FredThx/FERG/divers/arduino.PNG

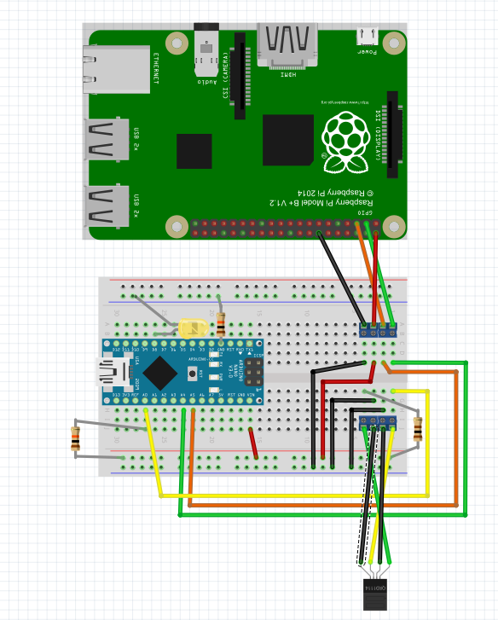
divers/arduino.PNG
