FredThx/FERG/divers/carte.png

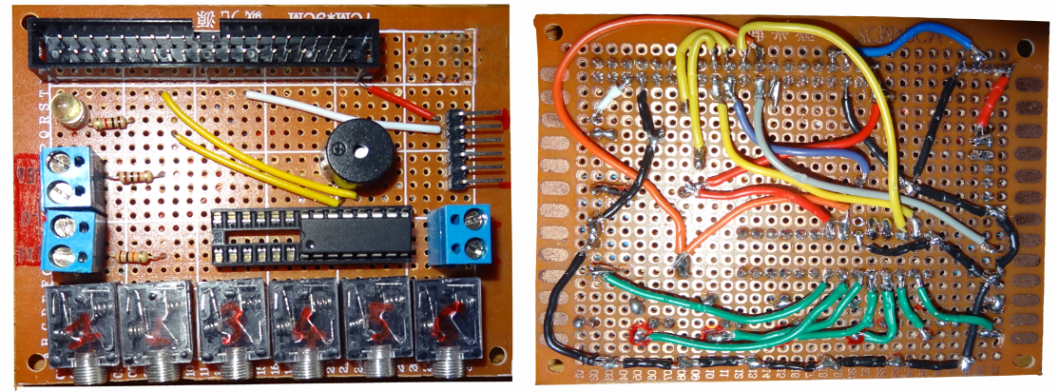
divers/carte.png
