FredThx/FERG/divers/detecteur_tension.jpg

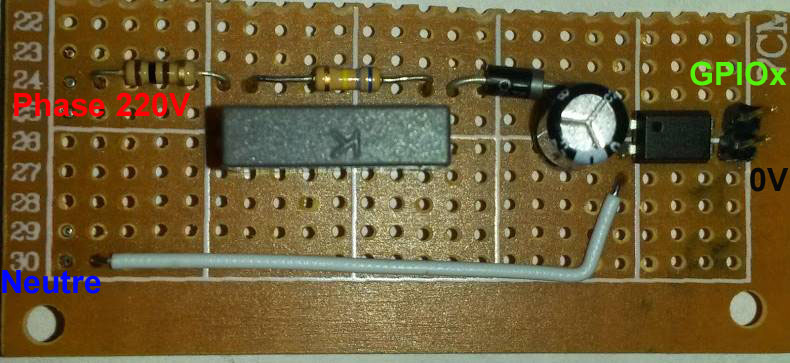
divers/detecteur_tension.jpg
