FredThx/FERG/divers/detection_secteur.png

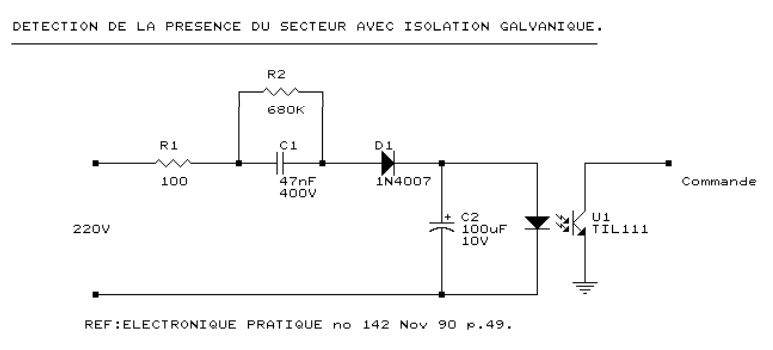
divers/detection_secteur.png
