FredThx/FERG/divers/DSC08218.png

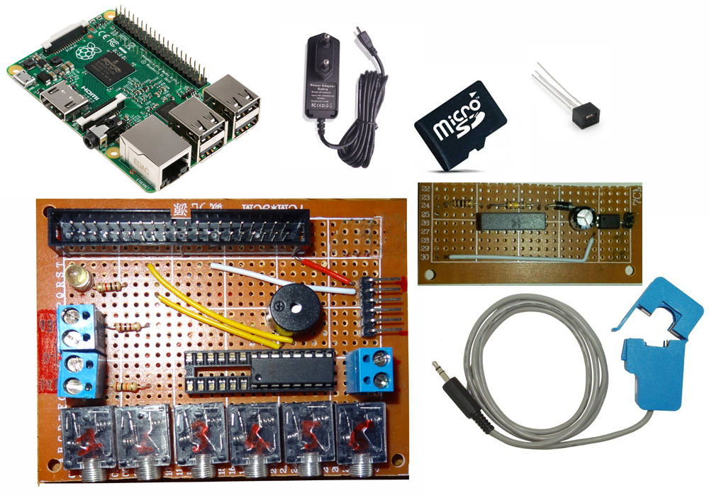
divers/DSC08218.png
