FredThx/FERG/divers/DSC08221.JPG

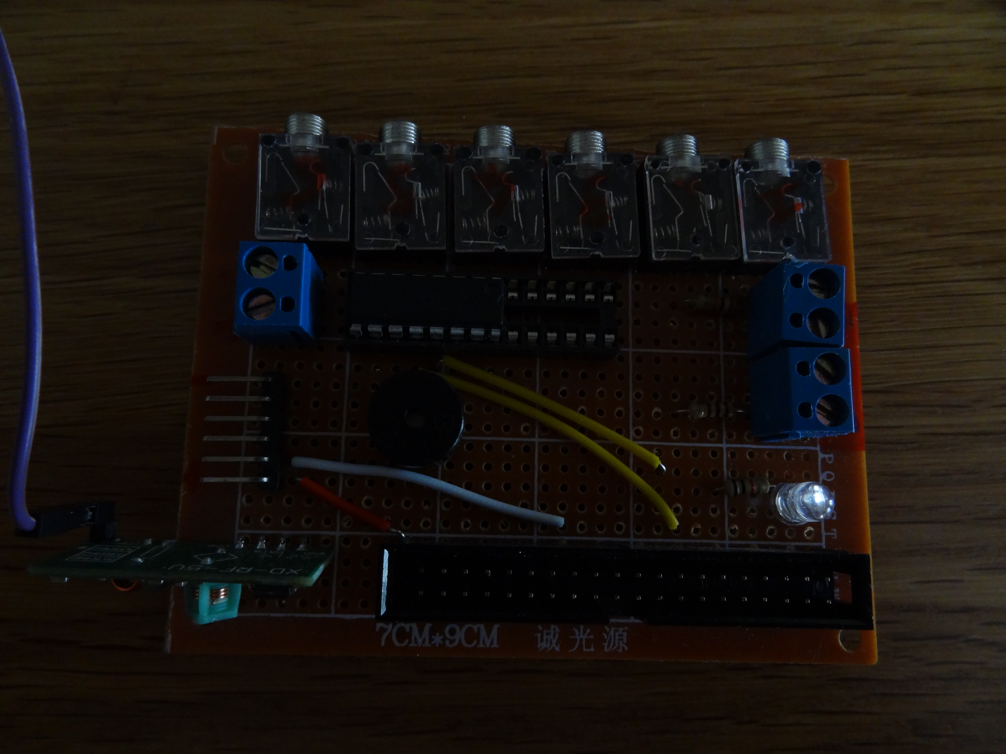
divers/DSC08221.JPG
