FredThx/FERG/divers/DSC09356.png

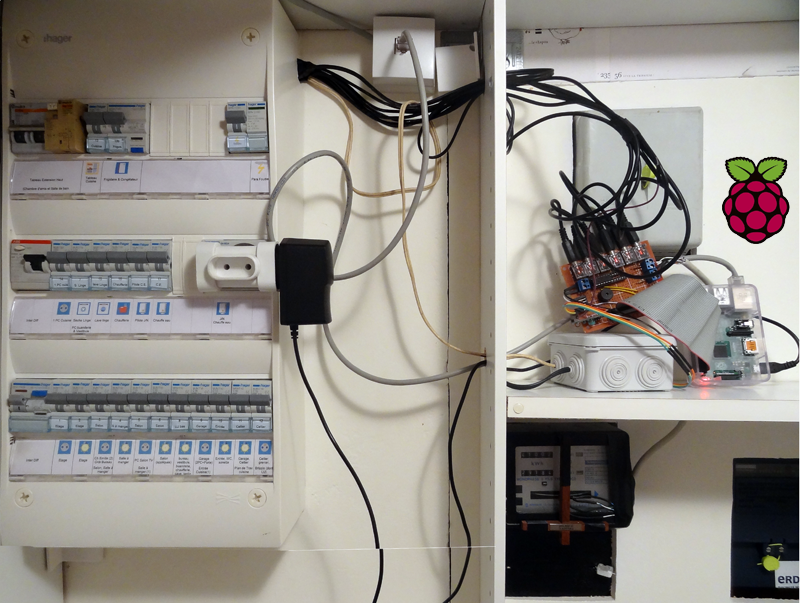
divers/DSC09356.png
