FredThx/FERG/divers/DSC09357.JPG

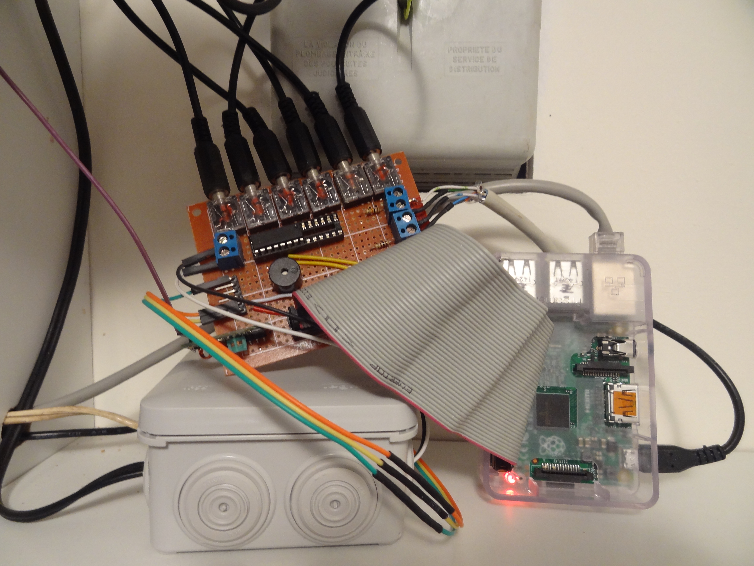
divers/DSC09357.JPG
