FredThx/FERG/divers/DSC09358.JPG

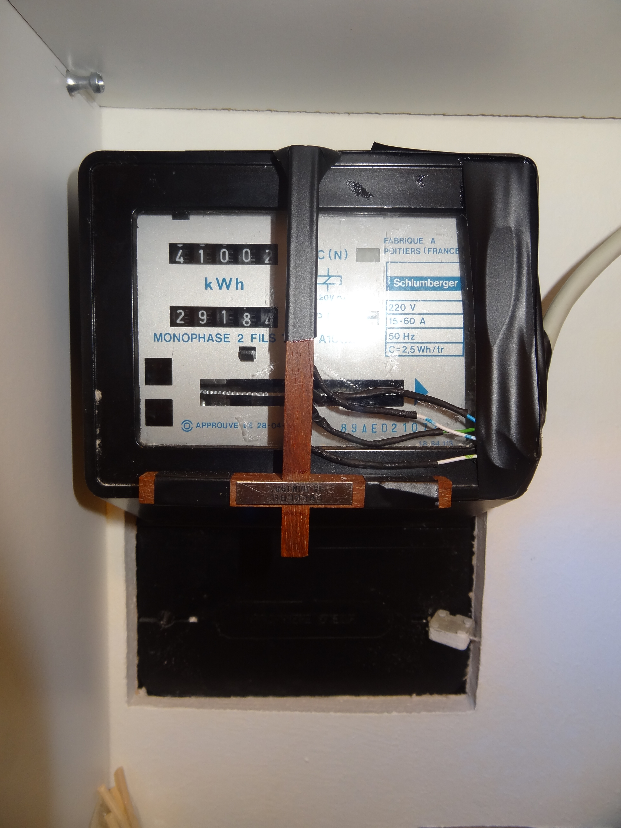
divers/DSC09358.JPG
