FredThx/FERG/divers/DSC09360.JPG

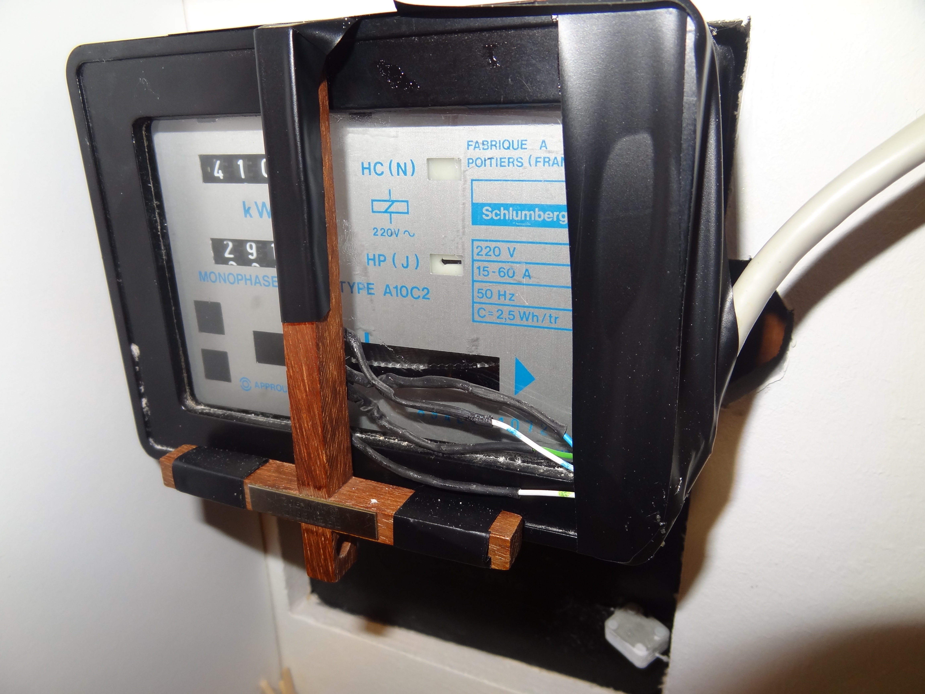
divers/DSC09360.JPG
