FredThx/FERG/divers/FERG sauf 433_circuit imprimé.png

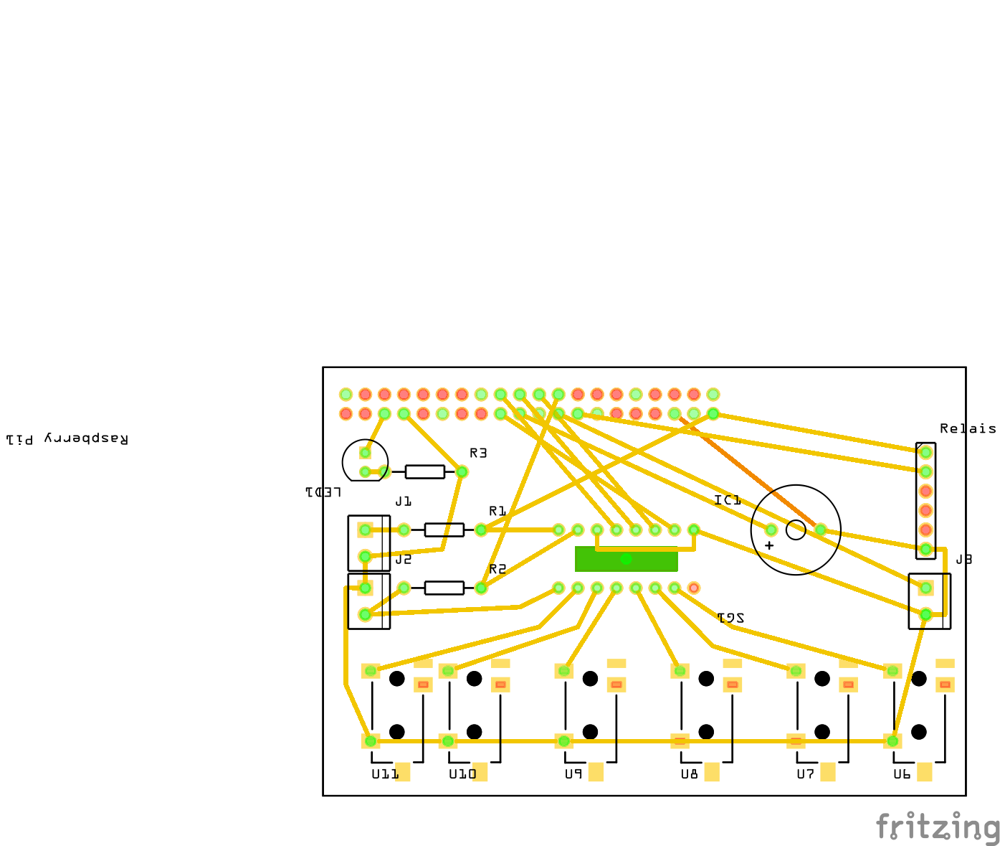
divers/FERG sauf 433_circuit imprimé.png
