FredThx/FERG/divers/FERG sauf 433_schéma.png

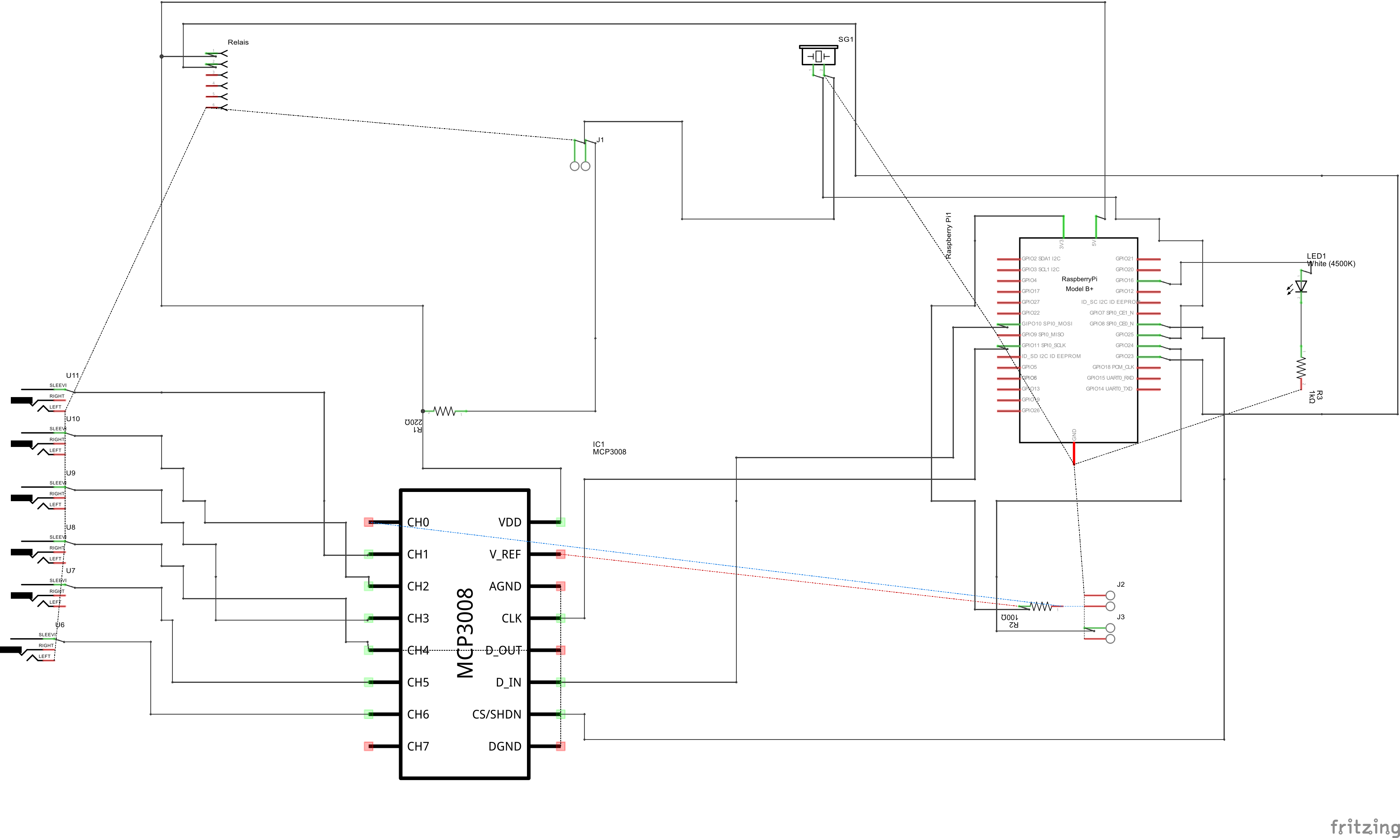
divers/FERG sauf 433_schéma.png
