FredThx/FERG/divers/FERG.JPG

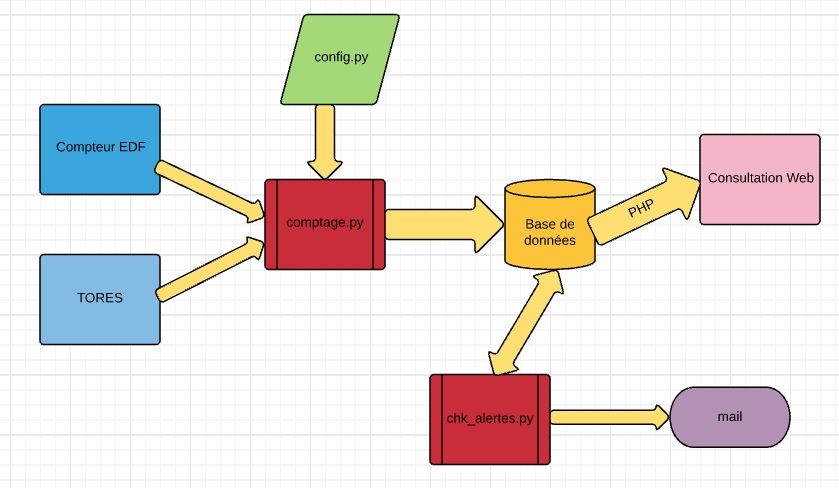
divers/FERG.JPG
