FredThx/FERG/divers/mcp3008.png

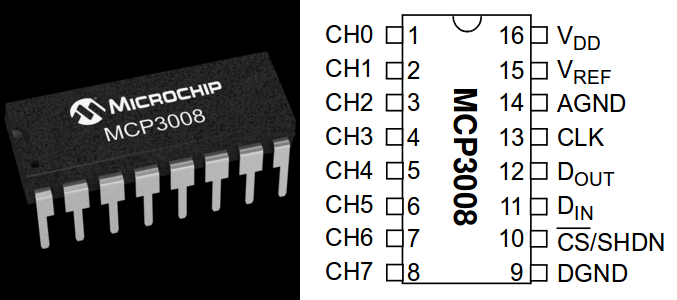
divers/mcp3008.png
