FredThx/FERG/divers/plexo.png

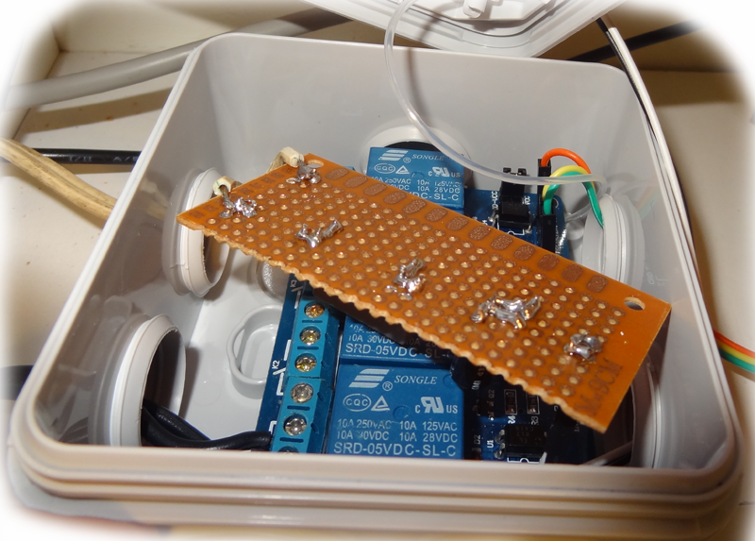
divers/plexo.png
