FredThx/FERG/divers/raspberry.png

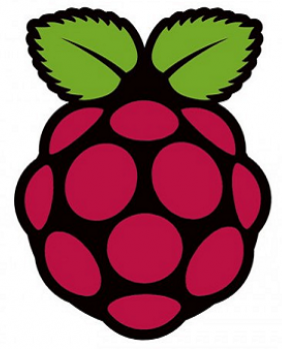
divers/raspberry.png
