FredThx/FERG/divers/relais.jpg

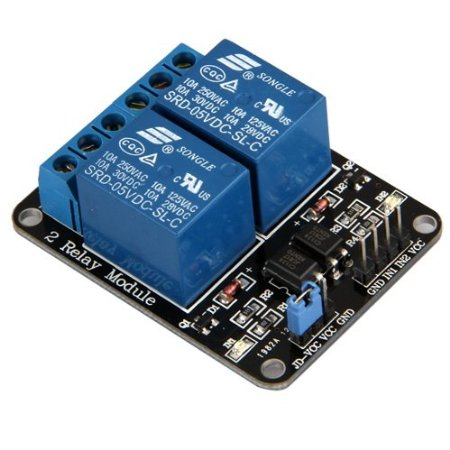
divers/relais.jpg
