FredThx/FERG/divers/synology.png

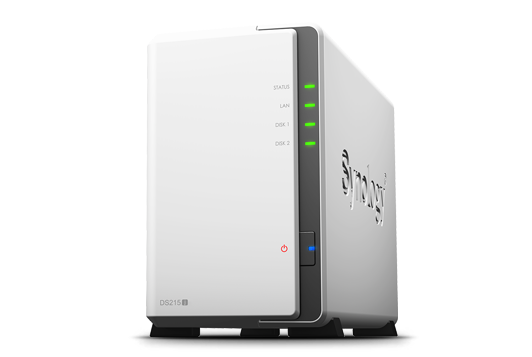
divers/synology.png
