FredThx/FERG/divers/tableau.png

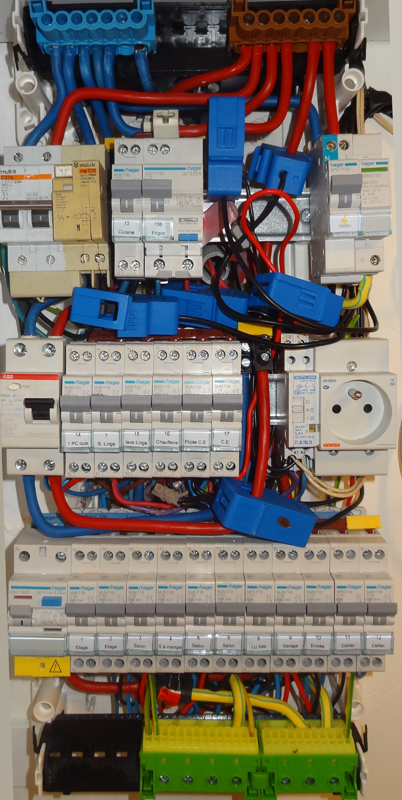
divers/tableau.png
