FredThx/FERG/divers/tore.png

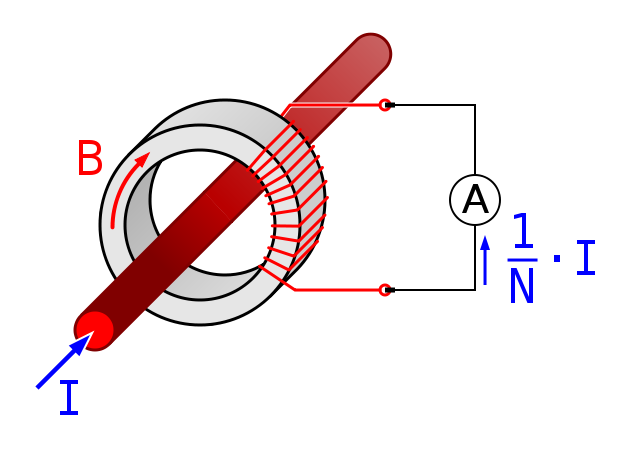
divers/tore.png
