FredThx/FERG/divers/web2.JPG

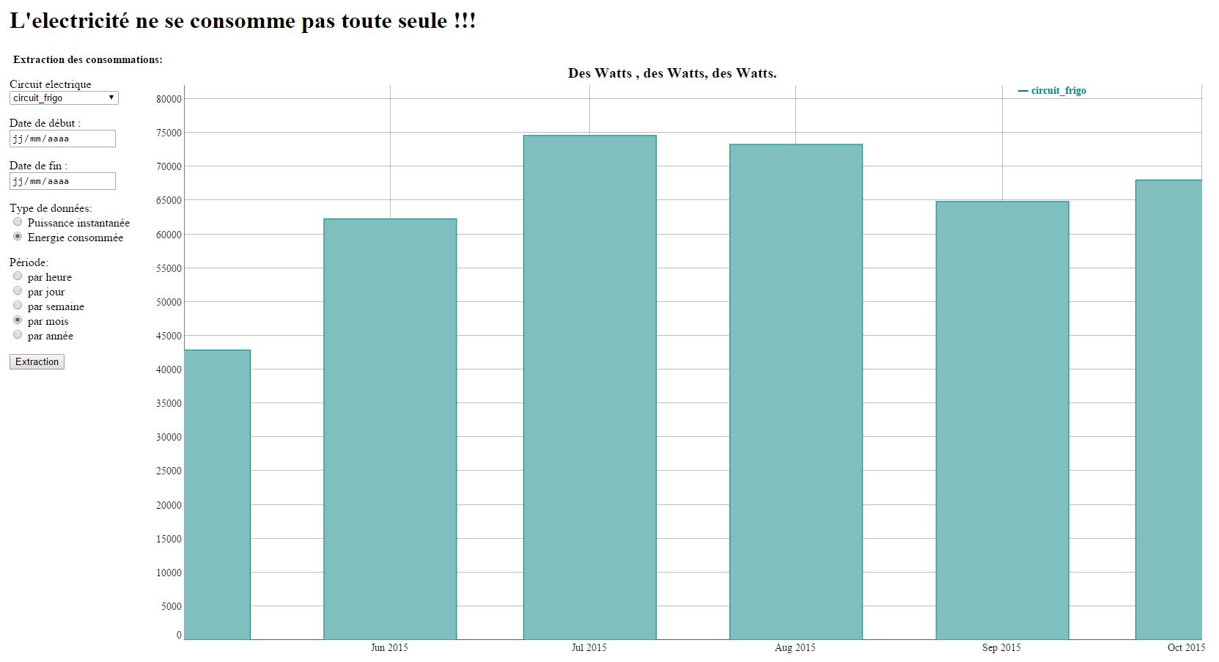
divers/web2.JPG
